rob-g2-365/waveshare_epaper_picture_frame/sdcard_image/pic_003.bmp

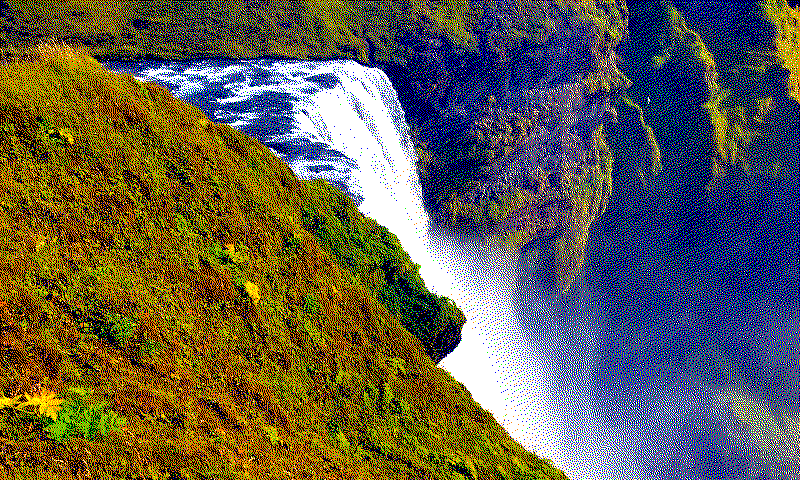
sdcard_image/pic_003.bmp
