rob-g2-365/waveshare_epaper_picture_frame/tests/images/IMG_20130702_134515.jpg

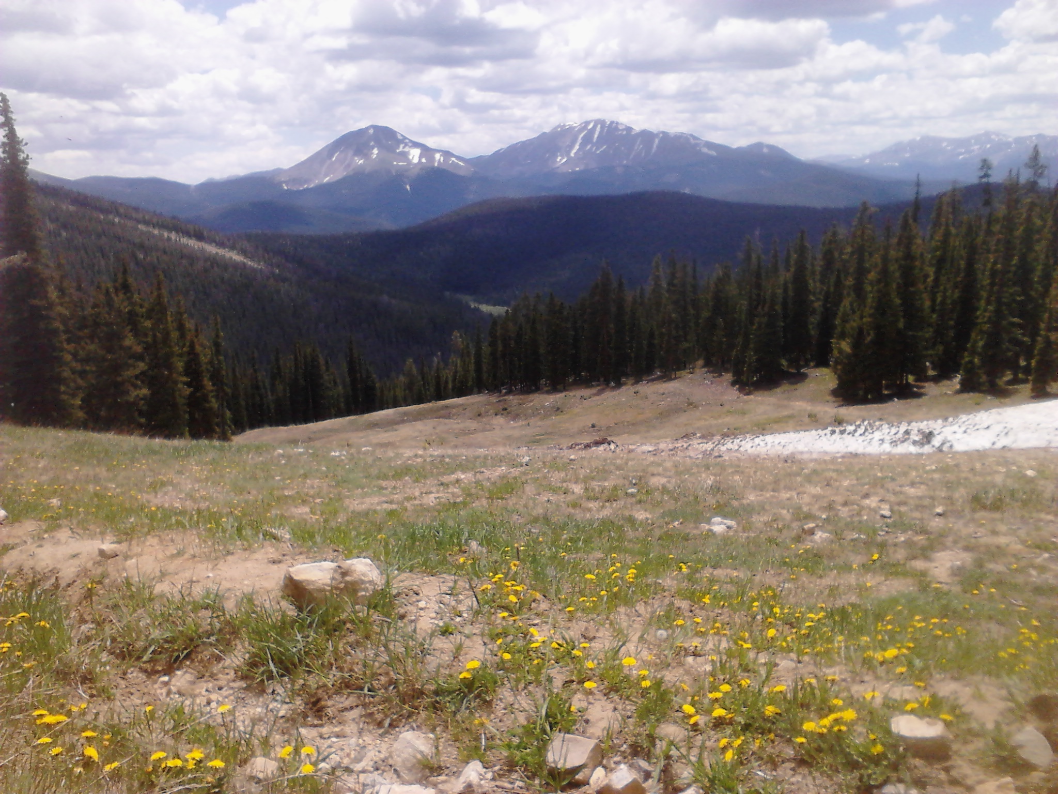
tests/images/IMG_20130702_134515.jpg
