rob-g2-365/waveshare_epaper_picture_frame/tests/images/subdir/DSCN6796.JPG

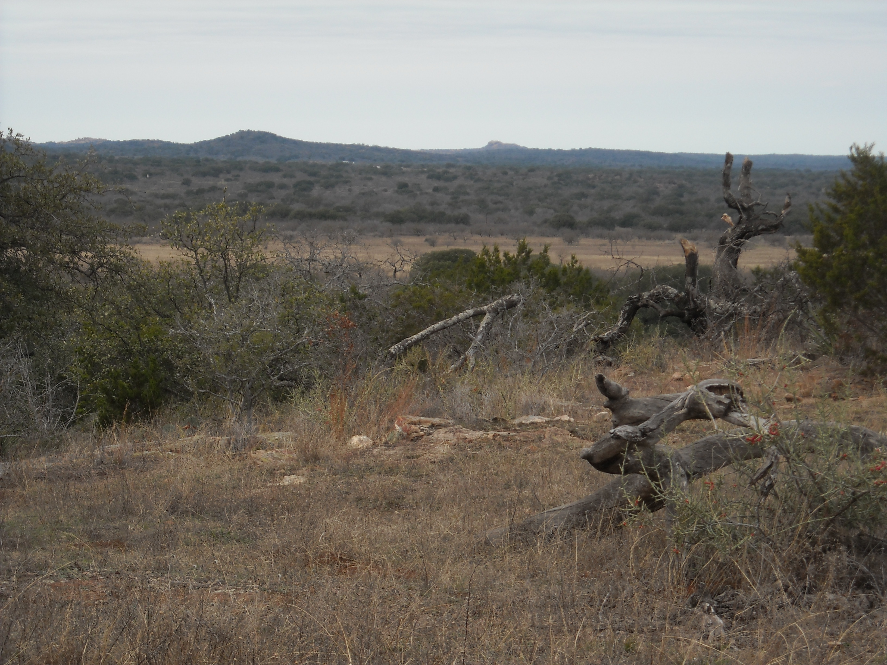
tests/images/subdir/DSCN6796.JPG
