rob-g2-365/waveshare_epaper_picture_frame/tests/images/subdir/DSCN6805.JPG

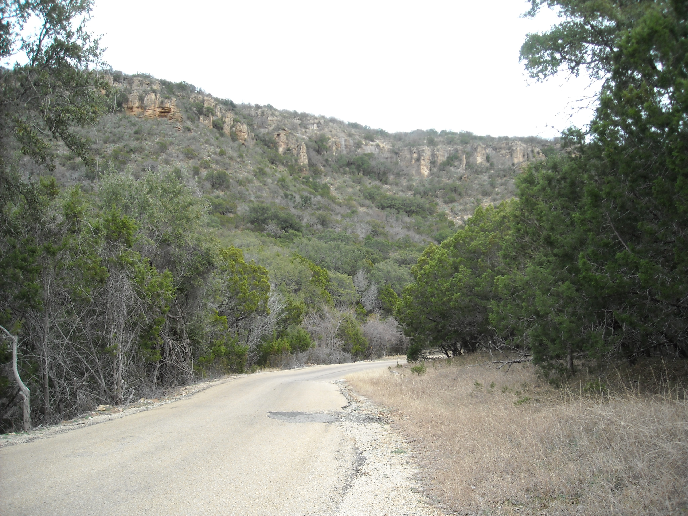
tests/images/subdir/DSCN6805.JPG
